Sychev-Lab/SychWire/Firmware/eddy/macros/SCREW_ADJUSTS.cfg

# █▀ █▄█ █▀▀ █░█ █▀▀ █░█
# ▄█ ░█░ █▄▄ █▀█ ██▄ ▀▄▀
# 
# Author: <Anton Sychev> (anton at sychev dot xyz) 
# .cfg (c) 2023 
# Created:  2023-08-21 02:06:08 
# Desc: Macros modifies

[gcode_macro SCREWS]
gcode:
  SCREWS_TILT_CALCULATE
