Sychev-Lab/SychWire/Firmware/eddy/macros/_START_PRINT.cfg

# █▀ █▄█ █▀▀ █░█ █▀▀ █░█
# ▄█ ░█░ █▄▄ █▀█ ██▄ ▀▄▀
# 
# Author: <Anton Sychev> (anton at sychev dot xyz) 
# .cfg (c) 2023 
# Created:  2023-08-21 02:06:08 
# Desc: Macros modifies
#----
#replace in pruse slicer start G-Code
#
#START_PRINT EXTRUDER_TEMP=[first_layer_temperature] BED_TEMP=[first_layer_bed_temperature]
#
#----

[gcode_macro START_PRINT]
gcode:
    {% set BED_TEMP = params.BED_TEMP|default(60)|float %}
    {% set EXTRUDER_TEMP = params.EXTRUDER_TEMP|default(190)|float %}
    
    G90 ; use absolute coordinates
    M83 ; extruder relative mode   
    G28 ; home all axis

    #bltouch
    #BED_MESH_CALIBRATE

    #eddy coil
    BED_MESH_CALIBRATE METHOD=scan SCAN_MODE=rapid 
    BED_MESH_PROFILE LOAD="default"
    
    G4 S30 ; allow partial nozzle warmup
    M190 S0 ; Prevents prusaslicer from prepending m190 to the gcode ruining our macro
    M109 S0 ; Prevents prusaslicer from prepending m109 to the gcode ruining our macro

    # Move XY to 0
    G1 X0 F6000
    G1 Y0 F6000
    
    # Move the nozzle near the bed
    G1 Z5 F3000
    # Move the nozzle very close to the bed
    G1 Z0.15 F300
    
    # Reset the G-Code Z offset (adjust Z offset if needed)
    SET_GCODE_OFFSET Z=0.0

    M104 S150 ; set temporary nozzle temp to prevent oozing during homing
    
    # Start bed heating
    M140 S{BED_TEMP}

    # Wait for bed to reach temperature
    M190 S{BED_TEMP}
    # Set and wait for nozzle to reach temperature
    M109 S{EXTRUDER_TEMP}

    # --------
    
    G1 Z3.0 F240
    G1 X2.0 Y10 F3000
    M104 S{EXTRUDER_TEMP} ; set final nozzle temp
    M190 S{BED_TEMP} ; wait for bed temp to stabilize
    M109 S{EXTRUDER_TEMP} ; wait for nozzle temp to stabilize
    G1 Z0.28 F240
    G92 E0
    G1 X2.0 Y140 E10 F1500 ; prime the nozzle
    G1 X2.3 Y140 F5000
    G92 E0
    G1 X2.3 Y10 E10 F1200 ; prime the nozzle
    G92 E0
