Sychev-Lab/SychWire/Firmware/bltoch/macros/NOTIFY.cfg

[gcode_macro NOTIFY]
gcode:
  {% if 'MSG' in params %}
    M117 {params.MSG}
    #RESPOND TYPE=command MSG="action:notification {params.MSG}"
  {% endif %}
